artiev/myog-backpack-guide/media/tables/baseweight-comparison-annapurna-scotland.tex

\begin{table}[H]
  \centering
  \begin{tabular}{ | l | p{3cm} | p{3cm} | }
    \hline			
    \textbf{Item} & \textbf{Himalayas} & \textbf{Scotland} \\
    \hline
    Approx. Base Weight & 9kg & 6.5kg \\
    \hline
    Days on the trail & 20 & 4 \\
    \hline
    Backpack & 1.1kg & 350 grams \\
    \hline
    Sleeping system & 1.5kg \newline (bag only) & 1.4kg \newline (full shelter) \\
    \hline
    Trekking Poles & 250 grams & N/A \\
    \hline
  \end{tabular}
  \caption{Base weight diet}
\end{table}
