artiev/myog-backpack-guide/media/images/design-drawings-2.jpg

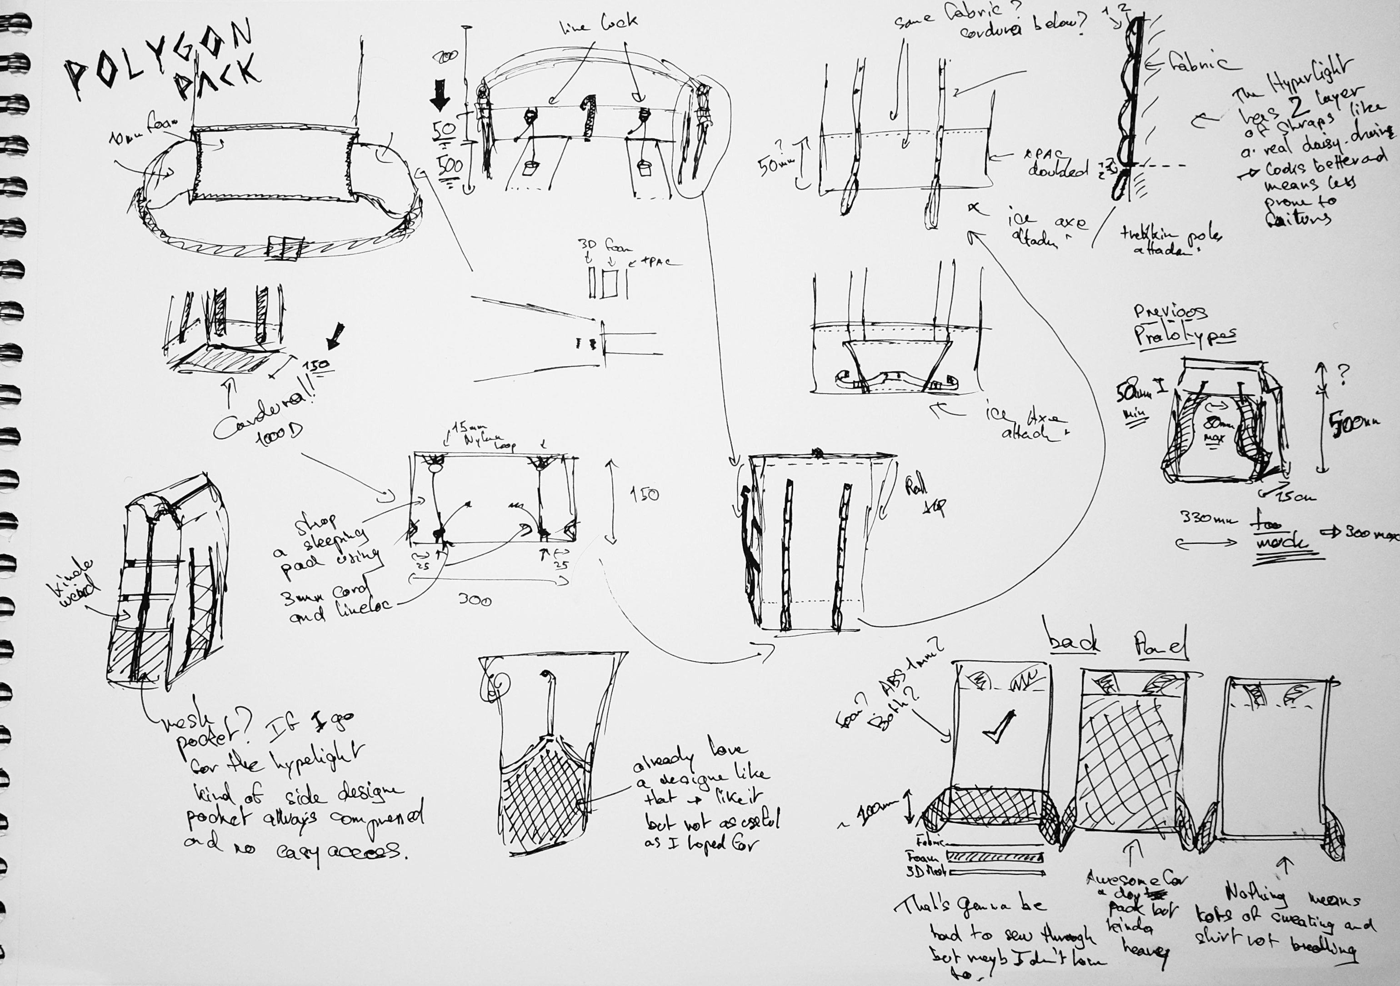
media/images/design-drawings-2.jpg
