artiev/myog-backpack-guide/media/images/highres/pack-bottom-cut.jpg

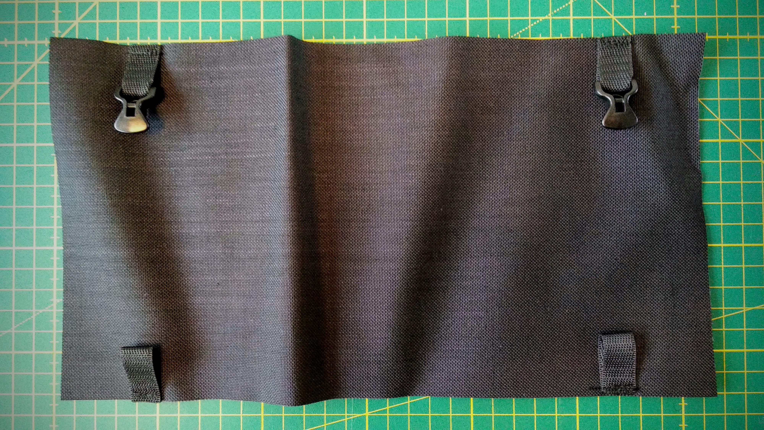
media/images/highres/pack-bottom-cut.jpg
