artiev/myog-backpack-guide/media/images/highres/workspace-1.jpg

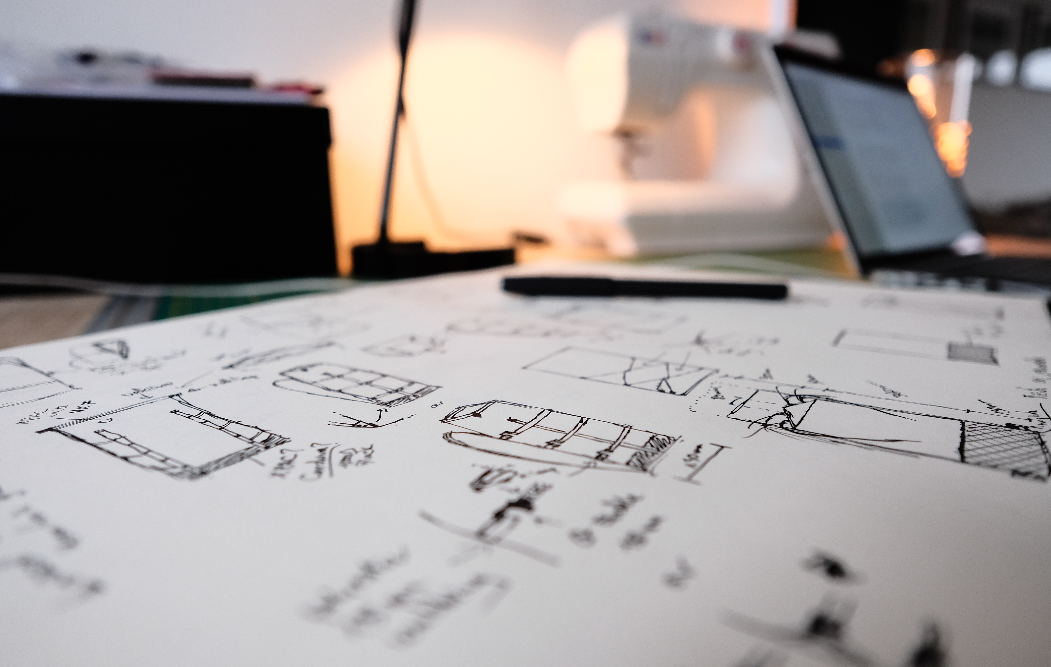
media/images/highres/workspace-1.jpg
